BehrensG/ETH1ISO224/SOFTWARE/ETH1ISO224/Core/BSP/Inc/DEVICE_INFO.h

/*
 * DEVICE_CFG.h
 *
 *  Created on: Jun 18, 2024
 *      Author: grzegorz
 */

#ifndef BSP_INC_DEVICE_INFO_H_
#define BSP_INC_DEVICE_INFO_H_

#define MANUFACTURER					"GB"
#define MODEL							"ETH1ISO224"
#define SOFTWARE_VERSION				"01.001"
#define MANUFACTURER_DESCRIPTION		"Voltage measurement card"
#define PASSWORD 						"ETH1ISO224"

#endif /* BSP_INC_DEVICE_INFO_H_ */
